james1236/pico-foldable/ssd1327.py

"""
MicroPython SSD1327 OLED I2C driver
https://github.com/mcauser/micropython-ssd1327

MIT License
Copyright (c) 2017 Mike Causer

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
from micropython import const
import time
import framebuf
from uos import uname


# commands
SET_COL_ADDR          = const(0x15)
SET_SCROLL_DEACTIVATE = const(0x2E)
SET_ROW_ADDR          = const(0x75)
SET_CONTRAST          = const(0x81)
SET_SEG_REMAP         = const(0xA0)
SET_DISP_START_LINE   = const(0xA1)
SET_DISP_OFFSET       = const(0xA2)
SET_DISP_MODE         = const(0xA4) # 0xA4 normal, 0xA5 all on, 0xA6 all off, 0xA7 when inverted
SET_MUX_RATIO         = const(0xA8)
SET_FN_SELECT_A       = const(0xAB)
SET_DISP              = const(0xAE) # 0xAE power off, 0xAF power on
SET_PHASE_LEN         = const(0xB1)
SET_DISP_CLK_DIV      = const(0xB3)
SET_SECOND_PRECHARGE  = const(0xB6)
SET_GRAYSCALE_TABLE   = const(0xB8)
SET_GRAYSCALE_LINEAR  = const(0xB9)
SET_PRECHARGE         = const(0xBC)
SET_VCOM_DESEL        = const(0xBE)
SET_FN_SELECT_B       = const(0xD5)
SET_COMMAND_LOCK      = const(0xFD)

# registers
REG_CMD  = const(0x80)
REG_DATA = const(0x40)


class SSD1327:
    def __init__(self, width, height, external_vcc):
        self.width = width
        self.height = height
        self.external_vcc = external_vcc
        self.buffer = bytearray(self.width * self.height // 2)
        self.framebuf = framebuf.FrameBuffer(self.buffer, self.width, self.height, framebuf.GS4_HMSB)
        self.poweron()
        self.init_display()

    def init_display(self):
        for cmd in (
            SET_COMMAND_LOCK, 0x12, # Unlock
            SET_DISP, # Display off
            # Resolution and layout
            SET_DISP_START_LINE, 0x00,
            SET_DISP_OFFSET, 0x20, # Set vertical offset by COM from 0~127
            # Set re-map
            # Enable column address re-map
            # Disable nibble re-map
            # Horizontal address increment
            # Enable COM re-map
            # Enable COM split odd even
            SET_SEG_REMAP, 0x51,
            SET_MUX_RATIO, self.height - 1,
            # Timing and driving scheme
            SET_FN_SELECT_A, 0x01, # Enable internal VDD regulator
            SET_PHASE_LEN, 0x51, # Phase 1: 1 DCLK, Phase 2: 5 DCLKs
            SET_DISP_CLK_DIV, 0x01, # Divide ratio: 1, Oscillator Frequency: 0
            SET_PRECHARGE, 0x08, # Set pre-charge voltage level: VCOMH
            SET_VCOM_DESEL, 0x07, # Set VCOMH COM deselect voltage level: 0.86*Vcc
            SET_SECOND_PRECHARGE, 0x01, # Second Pre-charge period: 1 DCLK
            SET_FN_SELECT_B, 0x62, # Enable enternal VSL, Enable second precharge
            # Display
            SET_GRAYSCALE_LINEAR, # Use linear greyscale lookup table
            SET_CONTRAST, 0x7f, # Medium brightness
            SET_DISP_MODE, # Normal, not inverted
            # 96x96:
            # SET_ROW_ADDR, 0 95,
            # SET_COL_ADDR, 8, 55,
            # 128x128:
            # SET_ROW_ADDR, 0 127,
            # SET_COL_ADDR, 0, 63,
            SET_ROW_ADDR, 0x00, self.height - 1,
            SET_COL_ADDR, ((128 - self.width) // 4), 63 - ((128 - self.width) // 4),

            SET_SCROLL_DEACTIVATE,
            SET_DISP | 0x01): # Display on
            self.write_cmd(cmd)
        self.fill(0)
        self.show()

    def poweroff(self):
        self.write_cmd(SET_FN_SELECT_A)
        self.write_cmd(0x00) # Disable internal VDD regulator, to save power
        self.write_cmd(SET_DISP)

    def poweron(self):
        self.write_cmd(SET_FN_SELECT_A)
        self.write_cmd(0x01) # Enable internal VDD regulator
        self.write_cmd(SET_DISP | 0x01)

    def rotate(self, rotate):
        self.poweroff()
        self.write_cmd(SET_DISP_OFFSET)
        self.write_cmd(self.height if rotate else self.offset)
        self.write_cmd(SET_SEG_REMAP)
        self.write_cmd(0x42 if rotate else 0x51)
        self.poweron()

    def contrast(self, contrast):
        self.write_cmd(SET_CONTRAST)
        self.write_cmd(contrast) # 0-255

    def invert(self, i):
        if (i == 0):
            i = 0xA4
        else:
            i = 0xA7
        self.write_cmd(SET_DISP_MODE | (i & 1) << 1 | (i & 1)) # 0xA4=Normal, 0xA7=Inverted

    def show(self):
        self.write_cmd(SET_COL_ADDR)
        self.write_cmd((128 - self.width) // 4)
        self.write_cmd(63 - ((128 - self.width) // 4))
        self.write_cmd(SET_ROW_ADDR)
        self.write_cmd(0x00)
        self.write_cmd(self.height - 1)
        self.write_data(self.buffer)

    def fill(self, col):
        self.framebuf.fill(col)

    def pixel(self, x, y, col):
        self.framebuf.pixel(x, y, col)
        
    def fill_rect(self, x, y, width, height, color):
        self.framebuf.fill_rect(x, y, width, height, color)

    def stroke_rect(self, x, y, width, height, color):
        self.framebuf.rect(x, y, width, height, color) #stroke_rect, or rect with f = False
        
    def blit(self, buffer, x, y, key, palette=None):
        if (palette == None):
            self.framebuf.blit(buffer, x, y, key)
        else:
            self.framebuf.blit(buffer, x, y, key, palette)

    def scroll(self, dx, dy):
        self.framebuf.scroll(dx, dy)
        # software scroll

    def text(self, string, x, y, col=15):
        self.framebuf.text(string, x, y, col)

    def line(self, x1, y1, x2, y2, col):
        self.framebuf.line(x1, y1, x2, y2, col)

    #Given a list of coordinates, draw an arbitrary (convex or concave) closed polygon at the given x, y location using the given color.
    #The coords must be specified as a array of integers, e.g. array('h', [x0, y0, x1, y1, ... xn, yn]).
    #The optional fill parameter can be set to True to fill the polygon. Otherwise just a one pixel outline is drawn.
    def poly(self, x, y, coords, col, fill=False):
        self.framebuf.poly(x, y, coords, col, fill)

    #Draw an ellipse at the given location. Radii xr and yr define the geometry; equal values cause a circle to be drawn. The c parameter defines the color.
    #The optional fill parameter can be set to True to fill the ellipse. Otherwise just a one pixel outline is drawn.
    #The optional quadrantBits parameter enables drawing to be restricted to certain quadrants of the ellipse.
    #The LS four bits determine which quadrants are to be drawn, with bit 0 specifying Q1, b1 Q2, b2 Q3 and b3 Q4.
    #Quadrants are numbered counterclockwise with Q1 being top right.
    def ellipse(self, x, y, xr, yr, col, fill=False, quadrantBits=0xF):
        self.framebuf.ellipse(x, y, xr, yr, col, fill, quadrantBits)


class SSD1327_I2C(SSD1327):
    def __init__(self, width, height, i2c, addr=0x3c, external_vcc=False):
        self.i2c = i2c
        self.addr = addr
        self.temp = bytearray(2)
        super().__init__(width, height, external_vcc)

    def write_cmd(self, cmd):
        self.temp[0] = REG_CMD # Co=1, D/C#=0
        self.temp[1] = cmd
        self.i2c.writeto(self.addr, self.temp)

    def write_data(self, buf):
        self.temp[0] = self.addr << 1
        self.temp[1] = REG_DATA # Co=0, D/C#=1
        # check if board is Pi Pico as it doesn't support start, write and stop operations.
        if uname()[0] == 'rp2':
            self.i2c.writeto(self.addr, b'\x40' + buf)
        else:
            self.i2c.start()
            self.i2c.write(self.temp)
            self.i2c.write(buf)
            self.i2c.stop()


class SEEED_OLED_96X96(SSD1327_I2C):
    def __init__(self, i2c):
        super().__init__(96, 96, i2c)

    def rotate(self, rotate):
        self.poweroff()
        self.write_cmd(SET_DISP_OFFSET)
        self.write_cmd(0x60 if rotate else 0x20) # 0x20=0 degrees, 0x60=180 degrees
        self.write_cmd(SET_SEG_REMAP)
        self.write_cmd(0x42 if rotate else 0x51) # 0x51=0 degrees, 0x42=180 degrees
        self.poweron()

    def lookup(self, table):
        # GS0 has no pre-charge and current drive
        self.write_cmd(SET_GRAYSCALE_TABLE)
        for i in range(0,15):
            self.write_cmd(table[i])


class WS_OLED_128X128(SSD1327_I2C):
    def __init__(self, i2c, addr=0x3c):
        super().__init__(128, 128, i2c, addr)
        self.write_cmd(SET_DISP_OFFSET)
        self.write_cmd(0x00)
