james1236/pico-foldable/creations/dog.py

from buzzer_music import music
import utime
import _thread
import framebuf

musicPlaying = False
mySong = None

def musicThread():
    global mySong
    global musicPlaying
    
    while True:
        utime.sleep(0.04)
        if (not musicPlaying):
            mySong.stop()
            del mySong
            break
        
        try:
            mySong.tick()
        except Exception:
            pass

#Optional metadata for main menu
class description:
    name = "Dog :)"
    thumbnail = bytearray(b"\x00\x00\x00\x00\x00\x00\x00\x00\x00\x00\x00\x00\x00\x00\x00\x00\x00\x00\x00\x00\x00\x00\x00\x00\x00\x00\x00\x00\x00\xbd\x00\x00\x01\x42\x80\x00\x01\x00\x80\x00\x01\x00\x40\x80\x02\x48\x61\x40\x02\x00\x19\x40\x02\x30\x07\x40\x02\xa4\x00\x40\x02\x78\x00\x40\x02\x00\x00\x40\x02\x00\x00\x40\x02\x00\x00\x40\x02\x00\x00\x40\x01\x00\x00\x80\x01\x33\xcc\x80\x01\x32\x4c\x80\x01\x54\x55\x00\x00\x88\x22\x00\x00\x00\x00\x00\x00\x00\x00\x00\x00\x00\x00\x00\x00\x00\x00\x00\x00\x00\x00\x00\x00\x00\x00\x00\x00\x00\x00\x00")

#Required class named 'creation'
class creation:
    def __init__(self, display, controller, *args): #Required init method in creation class
        global mySong
        global musicPlaying
        self.frame = 0
        self.display = display
        self.controller = controller
        
        data = bytearray(b"\x88\xa8\x8a\x8a\x8a\x8a\xaa\xaa\x8a\xaa\xaa\xaa\xaa\xaa\xaa\xaa\xaa\xaa\xaa\xaa\xaa\xaa\xaa\xaa\xaa\xaa\xaa\xaa\xaa\xaa\xaa\xaa\xaa\xaa\xaa\xaa\xaa\xaa\xaa\xaa\xaa\xaa\xaa\xaa\x8a\xa8\xa8\xa8\xa8\xa8\x8a\x88\x88\x88\x88\x88\x88\x88\x88\x88\x88\x88\x88\x88\xa8\x8a\x8a\x8a\x8a\xa8\xa8\xaa\xaa\x8a\xaa\xaa\xaa\xaa\xaa\xaa\xaa\xaa\xaa\xaa\xaa\xaa\xaa\xaa\xaa\xaa\xaa\xaa\xaa\xaa\xaa\xaa\xaa\xaa\xaa\xaa\xaa\xaa\xa8\xaa\x8a\x8a\x8a\x8a\xa8\xaa\xa8\xa8\xa8\x8a\x88\x8a\x88\x88\x88\x88\x88\x88\x88\x88\x88\x88\x88\x88\x88\xa8\xa8\xa8\xaa\x8a\xaa\xaa\xa8\xaa\xaa\xaa\xaa\xaa\xaa\xaa\xaa\xaa\xaa\xaa\xaa\xaa\xaa\xaa\xaa\xaa\xaa\xaa\xaa\xaa\xaa\xaa\xaa\xaa\xaa\xaa\xaa\xaa\xaa\xaa\xaa\xaa\xaa\xaa\x8a\xa8\x8a\x8a\x8a\x8a\x88\x8a\x88\x88\x88\x88\x88\x88\x88\x88\x88\x88\x88\x88\x8a\x8a\x8a\x8a\x8a\x8a\x8a\xaa\xaa\xaa\xaa\xaa\xaa\xaa\xaa\xaa\xaa\xaa\xaa\xaa\xaa\xaa\xaa\xaa\xaa\xaa\xaa\xaa\xaa\xaa\xaa\xaa\xaa\xaa\xaa\xaa\xaa\xa8\xaa\xaa\xaa\x8a\xa8\xaa\xa8\xaa\xa8\xa8\x8a\x88\xa8\x88\x88\x88\x88\x88\x88\x88\x88\x88\x88\x88\x88\x88\x8a\x8a\x8a\xaa\x8a\xaa\xaa\xa8\xaa\xaa\xaa\xaa\xaa\xaa\xaa\xaa\xaa\xaa\xaa\xaa\xaa\xaa\xaa\xaa\xaa\xaa\xaa\xaa\xaa\xaa\xaa\xaa\xaa\xaa\xaa\xaa\xaa\xaa\xaa\xaa\xa8\xaa\xaa\xa8\xa8\xa8\x8a\x8a\x8a\x88\xa8\x88\x88\x88\x88\x88\x88\x88\x88\x88\x88\x88\x88\x88\x8a\x8a\x8a\x8a\xaa\xa8\xaa\xaa\xaa\xaa\xaa\xaa\xaa\xaa\xaa\xaa\xaa\xaa\xaa\xaa\xaa\xaa\xaa\xaa\xaa\xaa\xaa\xaa\xaa\xaa\xaa\xaa\xaa\xaa\xaa\xaa\xaa\xaa\xaa\xaa\xaa\xaa\x8a\xaa\x8a\xa8\xa8\xa8\x8a\x88\x8a\x88\x88\x88\x88\x88\x88\x88\x88\x88\x88\x88\x88\x88\x8a\x8a\xaa\x8a\xa8\xaa\xaa\xaa\xaa\xaa\xaa\xaa\xaa\xaa\xaa\xaa\xaa\xaa\xaa\xaa\xaa\xaa\xaa\xaa\xaa\xaa\xaa\xaa\xaa\xaa\xaa\xaa\xaa\xaa\xaa\xaa\xaa\xaa\xaa\xaa\xaa\xaa\x8a\xa8\xaa\x8a\x8a\x8a\x8a\x8a\x88\x88\x88\x88\x88\x88\x88\x88\x88\x88\x88\x88\x88\x88\xa8\xa8\xaa\xaa\xaa\xaa\xaa\xaa\xaa\xaa\xaa\xaa\xaa\xaa\xaa\xaa\xaa\xaa\xaa\xaa\xaa\xaa\xaa\xaa\xaa\xaa\xaa\xaa\xaa\xaa\xaa\xa8\xaa\xaa\xaa\xaa\xaa\xaa\xaa\xaa\xaa\xaa\xaa\xaa\x8a\xaa\x8a\x8a\x88\x8a\x88\xa8\x88\x88\x88\x88\x88\x88\x88\x88\x88\x88\x88\x88\xa8\xaa\xa8\xaa\xaa\xaa\xaa\xaa\xaa\xaa\xaa\xaa\xaa\xaa\xaa\xaa\xaa\xaa\xaa\xaa\xaa\xaa\xaa\xaa\xaa\xaa\xaa\xaa\xbb\xbc\xbb\xcc\xec\xec\xcc\xcb\xba\xaa\xaa\xaa\xaa\xaa\xaa\xaa\x8a\xa8\xaa\x88\xa8\xa8\x88\x88\x88\x88\x88\x88\x88\x88\x88\x88\x88\x88\x88\x88\xa8\xaa\xaa\x8a\xaa\xaa\xaa\xaa\xaa\xaa\xaa\xaa\xaa\xaa\xaa\xaa\xaa\xaa\xaa\xaa\xaa\xaa\xaa\xaa\xaa\xac\xce\xee\xef\xff\xff\xfe\xef\xff\xef\xff\xfe\xee\xcc\xba\xaa\xaa\xaa\xaa\xaa\xaa\x8a\x8a\xa8\x8a\x8a\x88\x88\x88\x88\x88\x88\x88\x88\x88\x88\x88\x88\x88\xaa\xaa\xaa\xaa\xaa\xaa\xaa\xaa\xaa\xaa\xaa\xaa\xaa\xaa\xaa\xaa\xaa\xaa\xaa\xaa\xaa\xaa\xaa\xbc\xee\xee\xee\xee\xee\xee\xfe\xee\xfe\xee\xee\xee\xef\xee\xff\xfe\xeb\xaa\xaa\xaa\xa8\xaa\x8a\xab\xa8\xaa\xa8\x88\x88\x88\x88\x88\x88\x88\x88\x88\x88\x88\x88\x87\x8a\xaa\xaa\xaa\xaa\xaa\xaa\xaa\xaa\xaa\xaa\xaa\xaa\xaa\xaa\xaa\xaa\xaa\xaa\xaa\xaa\xaa\xbe\xee\xee\xee\xee\xee\xee\xee\xee\xee\xee\xee\xee\xfe\xee\xfe\xee\xee\xff\xfe\xba\xaa\xba\xaa\xab\xbb\xaa\xab\xaa\xa8\x88\x88\x88\x88\x88\x88\x88\x88\x88\x88\x88\x88\xaa\xaa\xaa\xaa\xaa\xaa\xaa\xaa\xaa\xaa\xaa\xaa\xaa\xaa\xaa\xbb\xaa\xaa\xaa\xaa\xaa\xce\xee\xee\xee\xee\xee\xee\xee\xee\xee\xee\xee\xee\xee\xee\xfe\xee\xee\xee\xee\xee\xff\xee\xcb\xaa\xbe\xee\xee\xec\xaa\xa8\x88\x88\x88\x88\x88\x88\x88\x88\x88\x88\x88\x77\xaa\xaa\xaa\xaa\xaa\xaa\xaa\xaa\xaa\xaa\xaa\xaa\xaa\xab\xba\xce\xca\xaa\xaa\xaa\xac\xee\xee\xee\xee\xee\xee\xee\xee\xee\xee\xee\xee\xee\xee\xee\xee\xef\xef\xef\xee\xfe\xee\xef\xee\xee\xef\xee\xee\xee\xcb\xaa\x88\x88\x88\x88\x88\x88\x88\x88\x88\x88\x78\x87\xaa\xaa\xaa\xaa\xaa\xaa\xaa\xaa\xaa\xaa\xaa\xaa\xbb\xcc\xcc\xee\xec\xce\xeb\xab\xce\xee\xee\xee\xee\xee\xee\xee\xee\xee\xee\xee\xee\xee\xee\xee\xef\xee\xfe\xef\xee\xee\xef\xef\xee\xef\xee\xee\xee\xee\xee\xba\xa8\x88\x88\x88\x88\x88\x88\x88\x88\x78\x78\x78\xaa\xaa\xaa\xaa\xaa\xaa\xaa\xaa\xaa\xaa\xaa\xaa\xbb\xce\xee\xee\xfe\xef\xee\xee\xee\xee\xee\xee\xee\xee\xee\xee\xee\xee\xee\xee\xee\xee\xee\xef\xee\xfe\xef\xef\xef\xef\xee\xfe\xef\xee\xee\xee\xee\xee\xee\xec\xb8\xaa\x88\x88\x88\x88\x88\x88\x88\x78\x78\x77\xaa\xaa\xaa\xaa\xaa\xaa\xaa\xaa\xaa\xaa\xaa\xab\xbb\xce\xee\xee\xee\xee\xfe\xee\xee\xee\xee\xee\xee\xee\xee\xee\xee\xee\xee\xee\xee\xee\xee\xee\xee\xfe\xff\xee\xfe\xef\xef\xee\xfe\xef\xef\xee\xee\xee\xee\xee\xca\x88\x88\x88\x88\x88\x88\x88\x88\x78\x78\x77\xaa\xaa\xaa\xaa\xaa\xaa\xaa\xaa\xaa\xaa\xab\xcc\xcc\xee\xee\xee\xee\xee\xee\xee\xee\xee\xee\xee\xee\xee\xee\xee\xee\xee\xfe\xee\xee\xee\xee\xee\xee\xef\xef\xef\xee\xfe\xfe\xfe\xef\xee\xfe\xee\xee\xee\xee\xee\xee\xb8\x88\x88\x88\x88\x88\x88\x78\x87\x78\x77\xaa\xaa\xaa\xaa\xaa\xaa\xaa\xaa\xaa\xaa\xbc\xce\xee\xee\xee\xee\xee\xee\xee\xee\xee\xee\xee\xee\xee\xee\xee\xee\xee\xee\xfe\xee\xee\xee\xee\xee\xee\xfe\xef\xef\xef\xee\xff\xee\xee\xef\xee\xfe\xee\xee\xee\xee\xee\xeb\x88\x88\x88\x88\x88\x87\x88\x77\x78\x77\xaa\xaa\xaa\xaa\xaa\xaa\xaa\xaa\xaa\xaa\xbb\xcc\xee\xee\xee\xee\xee\xee\xee\xee\xee\xee\xee\xee\xee\xee\xee\xee\xee\xee\xee\xee\xee\xee\xee\xee\xee\xef\xef\xee\xfe\xfe\xef\xfe\xfe\xee\xfe\xee\xee\xee\xee\xee\xee\xee\xa8\x88\x88\x88\x88\x88\x78\x78\x77\x77\xaa\xaa\xaa\xaa\xaa\xaa\xaa\xaa\xaa\xaa\xbb\xce\xee\xee\xee\xee\xee\xee\xee\xee\xee\xee\xee\xee\xee\xee\xee\xee\xee\xee\xee\xfe\xee\xee\xee\xfe\xee\xee\xee\xfe\xfe\xfe\xfe\xee\xfe\xee\xee\xef\xee\xee\xee\xee\xee\xee\xea\x88\x88\x88\x87\x78\x78\x78\x77\x77\xaa\xaa\xaa\xaa\xaa\xaa\xaa\xaa\xab\xbc\xce\xce\xee\xee\xee\xee\xee\xee\xee\xee\xec\xee\xee\xee\xee\xee\xee\xee\xee\xee\xee\xee\xee\xee\xee\xee\xef\xee\xee\xee\xee\xfe\xfe\xfe\xfe\xee\xfe\xee\xee\xee\xee\xee\xee\xee\xee\xa8\x88\x88\x88\x88\x78\x77\x77\x77\xaa\xaa\xaa\xaa\xaa\xaa\xaa\xaa\xbb\xee\xee\xee\xce\xce\xee\xee\xee\xee\xee\xce\xce\xcc\xce\xee\xee\xee\xee\xee\xee\xfe\xee\xee\xee\xee\xee\xee\xee\xee\xee\xfe\xef\xee\xfe\xfe\xee\xee\xee\xee\xee\xee\xee\xee\xee\xee\xee\xee\xba\x88\x88\x87\x78\x77\x77\x77\xaa\xaa\xaa\xaa\xaa\xaa\xaa\xbb\xce\xee\xee\xee\xee\xce\xce\xee\xee\xee\xce\xce\xce\xee\xce\xce\xee\xee\xee\xee\xee\xee\xee\xee\xee\xee\xee\xee\xee\xee\xee\xee\xee\xee\xfe\xef\xfe\xfe\xee\xee\xee\xee\xee\xee\xee\xee\xee\xee\xec\xa8\x87\x78\x77\x87\x77\x77\xaa\xaa\xaa\xaa\xaa\xab\xab\xcc\xee\xee\xcc\xcc\xce\xce\xce\xee\xee\xee\xce\xcc\xce\xee\xee\xee\xce\xec\xee\xee\xee\xee\xee\xee\xee\xee\xee\xee\xee\xee\xee\xee\xee\xfe\xfe\xef\xee\xee\xee\xee\xee\xee\xee\xee\xee\xee\xee\xee\xee\xeb\xaa\xbb\xcb\xcb\x87\x77\xaa\xaa\xaa\xaa\xaa\xab\xcc\xee\xec\xcc\xcc\xcc\xcc\xee\xee\xee\xce\xec\xcc\xcc\xcc\xce\xce\xee\xee\xee\xee\xee\xee\xee\xee\xee\xee\xee\xee\xee\xee\xee\xee\xee\xee\xee\xee\xee\xfe\xee\xee\xee\xee\xee\xee\xee\xee\xee\xee\xee\xee\xee\xee\xee\xcc\xba\xa8\x77\xaa\xaa\xaa\xab\xab\xbc\xce\xec\xcc\xcc\xcc\xcc\xcc\xce\xee\xee\xec\xcc\xcb\xcb\xcc\xce\xcc\xce\xee\xce\xee\xee\xee\xee\xee\xee\xee\xee\xee\xee\xee\xee\xee\xee\xee\xfe\xef\xee\xee\xee\xee\xee\xee\xee\xee\xee\xee\xee\xec\xcc\xee\xee\xee\xee\xee\xcb\xaa\x87\xaa\xaa\xaa\xab\xab\xbe\xec\xcc\xcb\xbb\xbb\xcc\xcc\xcc\xcc\xcc\xec\xcb\xcb\xcc\xce\xcc\xcc\xcc\xee\xce\xee\xee\xee\xee\xee\xee\xee\xcc\xee\xee\xee\xee\xee\xee\xfe\xef\xee\xee\xee\xee\xee\xee\xee\xee\xee\xee\xee\xec\xcc\xec\xee\xee\xee\xee\xee\xcc\xaa\xaa\xaa\xaa\xaa\xbb\xcc\xee\xec\xbb\xbb\xbc\xbc\xcb\xcc\xbc\xcc\xbb\xbb\xcb\xcb\xcc\xcc\xcb\xcc\xcc\xcc\xee\xee\xee\xee\xee\xee\xee\xee\xec\xee\xee\xee\xee\xee\xee\xef\xee\xee\xee\xee\xee\xee\xee\xee\xee\xee\xee\xee\xec\xcc\xcc\xee\xee\xee\xec\xcc\xee\xec\xa8\xaa\xab\xaa\xbc\xee\xee\xcc\xba\xbb\xbb\xab\xbb\xbc\xcc\xbc\xbc\xcb\xbb\xbc\xcc\xcc\xcc\xcb\xcc\xce\xee\xce\xee\xee\xee\xec\xee\xee\xee\xee\xee\xee\xee\xee\xfe\xff\xee\xee\xee\xee\xee\xee\xee\xee\xce\xee\xee\xee\xee\xcb\xcc\xec\xee\xee\xee\xcc\xee\xcc\xba\xaa\xba\xbc\xee\xec\xcc\xbb\xab\xaa\xaa\xab\xbb\xbb\xba\xbb\xbb\xaa\xbb\xbc\xbb\xba\xbb\xcc\xcc\xee\xee\xee\xee\xee\xee\xec\xee\xec\xec\xee\xee\xee\xee\xee\xee\xef\xee\xee\xee\xee\xee\xee\xee\xee\xce\xce\xce\xee\xee\xcc\xcb\xce\xcc\xcc\xec\xcc\xce\xec\xba\xcc\xee\xee\xcc\xcb\xbb\xaa\xaa\xaa\xaa\xab\xbb\xba\xbb\xaa\xaa\xaa\xab\xbb\xaa\xba\xba\xbb\xcc\xee\xee\xee\xee\xee\xee\xee\xee\xee\xec\xee\xee\xee\xee\xee\xef\xee\xfe\xee\xfe\xfe\xee\xee\xee\xee\xcc\xee\xee\xec\xee\xcc\xcb\xbc\xee\xcc\xce\xce\xcc\xee\xca\xee\xec\xcb\xcb\xbb\xbb\xaa\xaa\xaa\xaa\xab\xbb\xbb\xbc\xbc\xba\xaa\xaa\xba\xab\xab\xbc\xce\xee\xee\xee\xee\xee\xfe\xee\xee\xee\xee\xee\xee\xee\xee\xee\xee\xee\xee\xfe\xee\xee\xfe\xee\xee\xee\xee\xcc\xcb\xcb\xcc\xce\xec\xcb\xbb\xbe\xcc\xcb\xcc\xcc\xce\xec\xcc\xcc\xcb\xba\xab\xaa\xab\xaa\x8a\x88\xab\xaa\xaa\xba\xaa\xa8\x8a\xaa\xaa\xaa\xaa\xbc\xcc\xee\xce\xee\xee\xfe\xee\xee\xee\xee\xee\xee\xee\xee\xee\xee\xee\xee\xee\xee\xee\xef\xef\xee\xee\xee\xee\xec\xce\xec\xce\xce\xcc\xcc\xba\xbb\xcc\xbb\xbc\xbc\xcc\xcc\xcc\xcb\xaa\x8a\xaa\xaa\xaa\x88\x88\x8a\xbb\xab\xaa\x88\x88\x8a\xaa\xba\xba\xbb\xbc\xcc\xee\xee\xec\xee\xee\xee\xee\xee\xfe\xee\xee\xee\xee\xee\xee\xee\xee\xee\xee\xee\xee\xee\xfe\xfe\xee\xee\xee\xee\xca\xbb\xce\xee\xcc\xcc\xbb\xab\xbc\xca\xac\xcb\xbb\xcc\xcb\xba\xaa\xaa\x88\x8a\xa8\x8a\x88\x8a\xbb\xaa\xaa\x88\x8a\xaa\xaa\xbb\xba\xab\xbc\xee\xee\xec\xcc\xbe\xee\xee\xee\xef\xef\xee\xee\xee\xee\xee\xee\xee\xee\xee\xee\xee\xee\xee\xee\xfe\xee\xee\xee\xee\xce\xcc\xbc\xce\xee\xca\xcb\xab\xbb\xca\x8a\xbc\xbc\xbb\xba\xa8\x88\x88\x8a\xaa\x88\xa8\x88\xaa\xaa\xaa\xba\xbb\xba\x8a\xab\xaa\xab\xbb\xce\xee\xee\xee\xcb\xbc\xce\xee\xee\xee\xee\xee\xee\xee\xee\xee\xee\xee\xee\xee\xee\xee\xcc\xee\xee\xee\xff\xee\xee\xee\xcb\xbc\xce\xce\xec\xeb\xac\xca\xab\xbb\xaa\xbb\xbb\xbc\xba\x88\x88\x88\x8a\xaa\x8a\xa8\x8a\xaa\xab\xba\xaa\xbb\xa8\x8a\xab\xbb\xab\xcc\xce\xee\xee\xcb\xba\xab\xcc\xee\xee\xee\xee\xee\xee\xee\xee\xee\xee\xee\xee\xee\xee\xee\xcb\xee\xee\xee\xee\xee\xee\xee\xec\xbc\xce\xee\xcc\xec\xbb\xcb\xab\xcb\xaa\xab\xaa\xac\xaa\x88\x88\x88\xaa\xa8\x8a\x8a\xa8\xa8\xab\xaa\xbe\xb8\x88\x8a\xbb\xab\xbb\xbc\xce\xee\xce\xcb\xba\xaa\xab\xee\xee\xee\xee\xee\xee\xee\xee\xee\xee\xee\xee\xec\xec\xcc\xab\xcc\xce\xee\xee\xfe\xee\xee\xec\xbb\xce\xee\xcc\xcc\xcb\xbc\xba\xbb\xba\xab\xbb\xab\xaa\x88\x88\x8a\xaa\x88\xa8\x8a\xa8\xa8\xaa\xab\xba\xaa\x87\x8b\xba\xab\xbb\xce\xee\xee\xec\xab\xaa\xaa\x8b\xce\xee\xee\xee\xee\xee\xee\xec\xee\xee\xee\xee\xec\xcc\xbb\xaa\xaa\xcc\xee\xee\xee\xee\xee\xee\xcb\xae\xee\xec\xcc\xcc\xbb\xba\xbb\xba\xaa\xbb\xab\xa8\x88\x8a\xaa\x88\x88\xa8\xa8\x8a\xaa\xaa\xaa\xbb\xa8\x87\xaa\xaa\xba\xbb\xee\xce\xee\xcb\xba\x88\x88\x8a\xbc\xce\xee\xee\xee\xee\xee\xec\xee\xee\xee\xee\xec\xbb\xaa\xa8\x88\xa8\xac\xee\xee\xee\xee\xee\xbb\xbc\xee\xce\xbc\xcc\xcb\xba\xbb\xba\xab\xbc\xbb\xa8\x88\x8a\xa8\x88\x88\x88\xa8\xaa\xaa\xaa\xaa\xaa\xa8\x67\xaa\xaa\xab\xbc\xce\xcc\xcb\xca\xaa\x84\x86\x88\xaa\xcc\xee\xee\xee\xee\xee\xee\xee\xee\xee\xee\xec\xba\xa8\x86\x66\x8a\xba\xbe\xee\xee\xee\xec\xba\xbc\xce\xee\xcc\xcc\xcc\xbb\xbb\xba\xab\xbb\xcb\x88\x8a\xaa\xa8\x88\xa8\x8a\x8a\xaa\xaa\xaa\xaa\xaa\x87\x48\xba\xba\xbb\xbc\xcc\xba\xa8\x88\x88\x86\x67\x88\xab\xbc\xee\xef\xef\xee\xee\xee\xee\xee\xee\xee\xee\xca\x88\x74\x22\x66\x8e\xcc\xee\xee\xee\xee\xaa\xcb\xce\xee\xeb\xeb\xcc\xbb\xab\xba\xaa\xbb\xbc\x88\x8a\xaa\x88\x88\x88\x8a\x8a\xaa\xaa\xaa\xaa\xba\x86\x6a\xaa\xab\xbb\xbc\xbb\xba\xaa\xca\xa7\x66\x46\x78\xaa\xbe\xef\xef\xff\xee\xee\xee\xee\xee\xee\xee\xee\xbb\x88\x61\x67\x41\x14\xce\xcc\xee\xee\xee\xb8\xbc\xce\xee\xec\xcb\xcb\xbb\xbb\xaa\xaa\xbc\xbc\x8a\xaa\xaa\xa8\xa8\x88\x8a\xaa\xaa\xaa\xab\xab\xb8\x74\x8a\xab\xaa\xbb\xbc\xba\xaa\xce\x41\x11\x11\x44\x78\xaa\xee\xee\xef\xfe\xef\xee\xee\xee\xee\xee\xee\xee\xeb\x87\x42\x8a\x64\x11\x6e\xec\xee\xee\xce\xb8\x8a\xce\xee\xcc\xcb\xbb\xba\xba\xaa\xaa\xaa\xbc\x88\x8a\xaa\x88\xa8\x88\x8a\xaa\xaa\xaa\xab\xbb\xa8\x66\x8a\xab\xab\xba\xba\xaa\xac\xb4\x11\x14\x74\x24\x48\x8c\xee\xee\xef\xff\xef\xee\xee\xee\xee\xfe\xee\xee\xec\xc7\x22\x11\x41\x21\x2a\xee\xcc\xee\xec\xa7\xaa\xbc\xee\xec\xcb\xbb\xba\xaa\xaa\xaa\xba\xab\x88\x88\xaa\x8a\xa8\x88\x8a\xaa\xaa\xba\xbb\xbb\x88\x67\x8a\xaa\xaa\xab\xbb\xaa\xbc\x41\x14\x66\xab\x42\x48\x8c\xee\xee\xef\xff\xef\xee\xee\xfe\xfe\xee\xee\xef\xee\xeb\x22\x11\x11\x21\x16\xac\xbb\xce\xcc\xb6\x88\xcc\xce\xec\xbb\xab\xba\xaa\xaa\xaa\xaa\xbb\x88\x88\x8a\x8a\xa8\x88\x8a\xaa\xab\xab\xbb\xa8\x87\x68\x8a\xaa\xaa\xab\xba\xab\xb7\x11\x24\x42\x47\x41\x48\xee\xee\xee\xee\xff\xef\xfe\xee\xff\xff\xff\xff\xee\xee\xee\x84\x21\x11\x12\x47\xab\xbb\xbb\xbc\xb6\x78\xac\xce\xec\xbb\xba\xaa\xaa\xaa\xaa\xaa\xab\x88\x88\x88\x8a\x88\xaa\x8a\xaa\xaa\xab\xbb\x8a\x87\x48\x8a\x8a\xaa\xab\xaa\xaa\x82\x12\x41\x11\x12\x12\x7b\xbc\xfe\xee\xee\xff\xff\xfe\xef\xff\xff\xff\xff\xef\xee\xee\xe7\x44\x44\x44\x7a\xce\xba\xab\xbc\xb6\x48\x8b\xcc\xec\xcb\xba\x8a\xab\xaa\xaa\xab\xbb\x88\x88\x88\x88\x88\x8a\x8a\xaa\xaa\xbb\xba\x8a\x87\x68\x88\x8a\xaa\xaa\x88\x87\x42\x11\x12\x11\x11\x17\xbe\xee\xee\xee\xff\xff\xff\xef\xef\xfe\xff\xff\xff\xfe\xff\xee\xee\xa7\x46\x68\xac\xce\xca\xbb\xcc\xb6\x48\x88\xbc\xee\xcb\xba\xaa\xaa\xba\xaa\xaa\xba\x88\x88\x77\x88\x88\x8a\x8a\xaa\xaa\xbb\xba\x8a\x84\x48\x88\x8a\xaa\x88\x87\x87\x64\x44\x21\x12\x44\x8a\xbe\xee\xef\xfe\xff\xff\xff\xfe\xef\xfe\xff\xff\xff\xff\xfe\xee\xfe\xeb\xaa\xab\xbe\xee\xec\xce\xec\xb6\x26\x87\xab\xee\xcc\xaa\xaa\xba\xab\xaa\xaa\xba\x88\x78\x87\x77\x87\x88\x8a\x8a\xaa\xbb\xba\x78\x84\x48\x88\xa8\x88\x88\x8a\xaa\xa8\x77\x76\x77\x77\x8a\xee\xce\xee\xef\xef\xff\xff\xfe\xff\xff\xff\xff\xff\xff\xff\xfe\xee\xec\xbb\xbe\xee\xee\xee\xee\xee\xc6\x24\x87\x8a\xce\xec\xba\xaa\xaa\xaa\xaa\xab\xba\x88\x88\x77\x77\x77\x88\x88\x8a\xaa\xbb\xa8\x77\x62\x68\x8a\x88\x88\x88\xaa\xaa\xaa\x88\x88\x87\x88\xac\xee\xee\xfe\xef\xff\xff\xef\xee\xff\xff\xff\xff\xff\xff\xff\xff\xfe\xee\xcc\xbc\xee\xee\xee\xee\xee\xc4\x24\x77\x8a\xbe\xec\xcb\xab\xaa\xaa\xaa\xab\xba\x86\x67\x77\x68\x77\x78\x88\x8a\xaa\xbb\xa8\x47\x62\x47\x8a\x8a\xaa\xaa\xaa\xaa\xaa\xbb\xaa\xaa\xab\xec\xee\xee\xee\xff\xff\xff\xfe\xff\xff\xff\xff\xff\xff\xff\xff\xff\xee\xee\xee\xcc\xee\xee\xee\xee\xee\xe6\x22\x66\x78\xbe\xec\xbb\x8a\xaa\x8a\xab\xaa\xba\x77\x78\x78\x78\x77\x88\x88\xaa\xbb\xbb\xa7\x47\x44\x48\x8a\xaa\xaa\xaa\xaa\xaa\xab\xba\xbb\xba\xbb\xcc\xee\xee\xef\xff\xff\xff\xff\xfe\xff\xff\xff\xfe\xee\xef\xff\xff\xef\xee\xee\xee\xee\xee\xee\xee\xee\xe8\x24\x44\x68\xac\xec\xba\x88\x8a\xaa\xab\xaa\xb8\x87\x76\x67\x78\x77\x78\x88\xaa\xbb\xbb\x86\x46\x44\x47\x8a\xaa\xaa\xba\xaa\xaa\xbb\xbb\xbb\xcc\xcc\xce\xee\xee\xff\xff\xff\xff\xee\xff\xff\xff\xee\xef\xee\xee\xef\xff\xee\xee\xee\xee\xee\xee\xee\xee\xee\xea\x44\x44\x67\x8b\xee\xba\x88\x88\xaa\xab\xaa\xa8\x87\x76\x67\x77\x78\x88\x88\xab\xba\xba\x86\x66\x44\x47\x8a\xaa\xbb\xcb\xba\xab\xbb\xba\xac\xcc\xcc\xce\xee\xee\xfe\xff\xff\xff\xff\xfe\xee\xee\xee\xee\xef\xee\xef\xef\xff\xee\xee\xef\xee\xee\xee\xee\xee\xea\x26\x64\x47\x8a\xee\xca\x88\x88\xaa\xab\xaa\x88\x88\x76\x67\x78\x88\x88\x8a\xab\xbb\xb8\x87\x64\x44\x46\x8a\xbb\xbb\xbb\xbb\xab\xaa\xab\xce\xec\xce\xce\xee\xef\xee\xee\xfe\xee\xee\xee\xec\xcc\xbb\xce\xee\xee\xee\xee\xff\xff\xee\xef\xee\xee\xee\xee\xef\xeb\x44\x76\x47\x8a\xce\xeb\x88\x88\xaa\xab\xba\x88\xa8\x76\x66\x76\x78\x88\x8a\xbb\xba\xb8\x86\x64\x44\x47\xaa\xab\xbb\xbb\xbb\xaa\xaa\xbc\xec\xcc\xcc\xcc\xee\xee\xee\xef\xff\xfe\xec\xbb\xbb\xaa\x8a\xaa\xce\xee\xee\xee\xff\xfe\xee\xee\xef\xfe\xee\xee\xee\xee\x44\x47\x46\x7a\xbe\xeb\xa8\x88\xab\xbb\xa8\x88\xa8\x87\x66\x67\x77\x88\xab\xbb\xbb\xa8\x76\x44\x44\x47\xab\xbc\xbc\xbb\xba\xba\xab\xcc\xcb\xce\xcc\xcc\xee\xee\xee\xee\xee\xee\xca\xa8\x87\x77\x88\x88\xac\xee\xce\xee\xef\xff\xee\xee\xee\xee\xee\xee\xee\xee\x64\x46\x44\x78\xbe\xec\xa8\xaa\xab\xba\xa8\x88\xba\x88\x66\x67\x77\x88\xaa\xbb\xbb\xa7\x74\x44\x44\x78\xaa\xbb\xbc\xbb\xab\xab\xbc\xcb\xce\xec\xcc\xce\xee\xee\xee\xec\xee\xec\xa8\x67\x66\x76\x64\x66\x78\xab\xcc\xee\xef\xff\xee\xee\xee\xef\xee\xee\xee\xee\x74\x46\x64\x68\xac\xec\xba\xaa\xbb\xba\xa8\x88\xba\xa8\x76\x66\x67\x88\xab\xbb\xbb\x88\x74\x44\x44\x8a\xaa\xbb\xba\xbb\xbb\xbb\xbb\xcc\xee\xec\xbb\xce\xee\xee\xee\xeb\xbc\xb8\x66\x66\x66\x66\x64\x46\x77\x68\xcc\xee\xef\xff\xfe\xee\xee\xee\xee\xee\xee\xee\x82\x47\x76\x67\xac\xee\xba\xab\xbb\xba\x88\x88\xba\xa8\x77\x66\x68\x88\xac\xbb\xba\x88\x74\x44\x46\x88\xab\xbb\xbb\xba\xab\xbb\xcc\xce\xec\xcb\xbc\xee\xee\xfe\xee\xee\xcb\x84\x66\x66\x64\x44\x64\x66\x46\x86\x8c\xce\xee\xff\xff\xee\xee\xee\xee\xee\xee\xee\xa4\x48\x87\x46\x8c\xee\xca\xab\xbb\xa8\x88\x88\xca\xb8\x88\x66\x78\x8a\xab\xbb\xba\x7a\x87\x44\x47\x8a\xab\xbb\xba\xaa\xaa\xbc\xbe\xee\xcb\xaa\xce\xce\xee\xee\xee\xeb\xa8\x44\x64\x44\x64\x66\x44\x66\x64\x68\x7a\xbe\xee\xff\xfe\xee\xee\xee\xee\xee\xee\xee\xb4\x68\xa8\x66\x7b\xee\xeb\xab\xba\xa8\xaa\x88\xbb\xba\x87\x67\x88\x8a\xbb\xbb\xa8\x8b\xa7\x66\x67\x8a\xaa\xab\xaa\xaa\xaa\xbb\xee\xcc\xbc\xbb\xcc\xce\xee\xee\xcb\xba\xa4\x46\x44\x44\x67\x67\x67\x77\x67\x77\x78\xac\xee\xff\xfe\xee\xec\xcc\xee\xee\xee\xec\xc4\x68\xa8\x76\x7a\xce\xeb\xbb\xba\x8a\x88\x88\xbb\xba\xa8\x77\x88\xaa\xbb\xbc\xa8\xab\xa7\x66\x47\x8a\xaa\xab\xab\xaa\xaa\xbe\xec\xec\xba\xbb\xbc\xce\xee\xee\xcb\xa8\x74\x74\x44\x44\x44\x44\x44\x44\x24\x24\x77\x8b\xef\xff\xff\xee\xec\xcc\xce\xee\xee\xee\xa4\x68\xaa\x87\x78\xce\xec\xbb\xaa\xa8\xa8\xa8\xbb\xba\x88\x77\x88\xaa\xbb\xbb\x88\xbc\xa8\x64\x67\x8a\xaa\xba\xba\xaa\xab\xce\xcc\xcb\xba\xcb\xbc\xee\xee\xee\xcb\xa8\x26\x42\x11\x11\x12\x21\x11\x11\x11\x11\x26\x8b\xee\xef\xff\xee\xee\xcc\xcc\xce\xee\xce\xa4\x67\xaa\xa7\x78\xae\xec\xcb\xaa\x88\xa8\x88\xbb\xba\xa8\x78\x88\xaa\xbc\xba\x7a\xcc\xa8\x66\x46\x8a\xaa\xaa\xaa\xaa\xbc\xcc\xcc\xcc\xaa\xbb\xbc\xee\xee\xcc\xcb\x88\x44\x11\x11\x11\x11\x11\x11\x11\x11\x11\x22\x8a\xce\xef\xff\xfe\xee\xcc\xcc\xce\xec\xce\xa4\x68\x8a\xa8\x78\x8c\xee\xcc\xa8\xaa\x8a\x88\xbb\xbb\xa8\x88\x8a\xaa\xbb\xb8\x8c\xcb\xa8\x66\x46\x8a\xaa\xab\xaa\xaa\xcb\xbb\xcc\xcb\xaa\xab\xbc\xcc\xec\xee\xeb\xa7\x42\x11\x11\x11\x11\x11\x11\x11\x11\x11\x16\x7a\xce\xff\xfe\xff\xee\xcb\xab\xcc\xcc\xce\xb7\x67\x8a\x88\x78\x8b\xee\xee\xba\x8a\x88\x8a\xbb\xbb\xaa\x88\x8a\xab\xbb\xb7\xac\xcb\xa8\x76\x47\x8a\xab\xaa\xaa\xaa\xbb\xbb\xcc\xba\xaa\xab\xbc\xce\xcc\xcc\xcb\x87\x44\x11\x11\x11\x12\x11\x11\x11\x11\x12\x44\x8a\xce\xef\xef\xef\xee\xec\xba\xac\xcc\xce\xb7\x66\x88\xa8\x87\x8b\xcc\xec\xca\xa8\xaa\x88\xbb\xbb\xba\x88\xaa\xbb\xab\xa7\xcc\xcb\xa8\x76\x66\x8a\xaa\xaa\xaa\xab\xbb\xbb\xbb\xaa\xbb\xcb\xce\xce\xec\xbb\xaa\xa8\x64\x11\x11\x11\x24\x11\x11\x44\x11\x66\x44\x6a\xce\xff\xef\xee\xfe\xec\xcb\xbb\xbb\xbc\xc7\x76\x78\xaa\xa8\x8b\xcc\xcc\xca\xa8\xa8\x8a\xbb\xbb\xba\x88\xaa\xbb\xba\x8a\xcc\xcb\xaa\x87\x66\x8a\xaa\x88\x88\x8a\xaa\xaa\xa8\x88\xaa\xbb\xec\xcc\xec\xcc\xbc\xca\x77\x66\x64\x21\x12\x11\x11\x48\x76\x84\x46\x7b\xce\xee\xee\xfe\xec\xcb\xcb\xbb\xcc\xce\xb8\x78\x78\xaa\xa8\x8b\xce\xcc\xca\xaa\x8a\x88\xbb\xbc\xba\xaa\xaa\xba\xaa\x8c\xcc\xcc\xba\x88\x76\x88\xaa\xa8\x88\x8a\xaa\xaa\xa8\xaa\xaa\xac\xec\xcc\xcc\xcc\xeb\xa8\x87\x76\x46\x64\x11\x11\x11\x12\x24\x44\x47\x8a\xbc\xee\xee\xfe\xfe\xbb\xbb\xac\xce\xce\xc7\x78\x88\xaa\xa8\x8a\xce\xec\xeb\xaa\x8a\x8a\xbb\xbb\xba\xaa\xab\xba\xa8\xac\xcc\xcc\xba\x88\x76\x8a\xa8\x88\xa8\x8a\x8a\xa8\x8a\xaa\xaa\xbe\xee\xee\xcc\xcc\xba\xa8\x88\x44\x24\x42\x11\x12\x11\x11\x12\x44\x67\x8a\xbe\xee\xee\xee\xee\xcb\xcb\xbc\xcc\xcc\xc8\x78\x8a\xaa\xaa\x88\xae\xce\xec\xa8\xa8\xa8\xbb\xbb\xaa\xaa\xbb\xaa\xa7\xbb\xcc\xee\xca\xa8\x77\x8a\x88\xa8\xa8\x8a\x88\x88\xaa\x8a\xaa\xbc\xcc\xcb\xba\xbb\xaa\xaa\x88\x66\x22\x12\x11\x11\x11\x11\x11\x44\x47\x8a\xbc\xce\xce\xef\xef\xcc\xcc\xee\xee\xcc\xb8\x88\x8a\xcc\xba\xa8\x8c\xec\xee\xa8\xa8\xa8\xbb\xbb\xab\xbb\xba\xaa\x8a\xcc\xce\xee\xba\x88\x86\x8a\xa8\xa8\x88\x88\x88\x88\x88\x88\xaa\xbc\xcc\xba\xab\xbb\xab\xaa\x78\x66\x44\x21\x11\x12\x11\x21\x24\x44\x48\x8a\xaa\xbc\xee\xee\xef\xcb\xcc\xce\xee\xcc\xa8\x88\x88\xac\xca\xa8\x78\xce\xcc\xb8\xaa\xaa\xbb\xbb\xbb\xbb\xba\xa8\x7c\xcc\xee\xee\xba\xa8\x87\x8a\x88\x88\xaa\x88\x88\x88\xaa\xaa\xaa\xcc\xcc\xba\x88\x8a\xaa\x88\xaa\x87\x64\x42\x44\x12\x12\x44\x44\x44\x76\x78\xbb\xce\xee\xee\xef\xcb\xcc\xee\xec\xcc\xaa\xa8\x88\x8c\xec\xaa\x87\xae\xce\xba\xaa\x8a\xbb\xbb\xbb\xab\xaa\x87\xbc\xbe\xee\xee\xeb\xaa\x88\x88\x88\xaa\xaa\xa8\x88\xaa\xaa\xa8\xaa\xcc\xcc\xcc\xbb\xaa\x8a\xaa\xa8\x87\x86\x64\x44\x41\x12\x44\x44\x44\x68\x48\xab\xcc\xee\xee\xee\xcb\xcc\xce\xeb\xbb\xaa\xaa\x8a\xbe\xcc\xba\xa8\x77\xae\xcc\xaa\x8a\xbb\xbb\xba\xaa\x88\x7b\xcc\xce\xee\xee\xec\xba\x88\x88\x8a\xaa\xaa\xa8\x88\xaa\x88\x8a\xaa\xbb\xcb\xba\xbb\xaa\xaa\xba\x88\xa7\x66\x64\x44\x42\x14\x44\x44\x44\x66\x8a\xab\xec\xee\xee\xee\xbb\xec\xcc\xcc\xca\xaa\xaa\xab\xee\xec\xba\xaa\xa8\x68\xcb\xba\xaa\xbb\xbb\xaa\xa8\x88\xbc\xbc\xce\xee\xee\xee\xba\x88\x88\x88\xa8\xaa\xaa\x88\x88\x88\xaa\x8a\xab\xca\xaa\xaa\xba\x8a\xaa\x88\x86\x66\x44\x44\x62\x24\x44\x44\x44\x67\x8a\xaa\xbb\xbc\xee\xee\xcc\xcc\xbc\xcb\xbb\xaa\xaa\xac\xee\xee\xcb\xaa\xaa\xa8\xac\xaa\x8a\xbb\xba\xa8\x88\x6a\xcb\xce\xee\xee\xee\xec\xba\xa8\x88\x88\x88\xaa\xa8\x88\xa8\x8a\x87\x8a\xac\xba\xab\xaa\xaa\xaa\xa8\xa7\x66\x46\x44\x46\x44\x22\x44\x44\x46\x68\x88\xbc\xbb\xee\xee\xee\xcc\xcb\xbb\xbb\xaa\xaa\xaa\xbc\xee\xee\xeb\xaa\xaa\xab\xbb\xaa\xaa\xbb\xba\xaa\x78\xac\xcc\xce\xee\xee\xee\xec\xcb\xaa\x88\x88\x88\x8a\x88\x8a\x88\xa7\x77\x8a\x8b\xbb\xba\xa8\x88\x8a\x78\x88\x77\x74\x66\x46\x44\x44\x44\x44\x46\x64\x8b\xab\xce\xce\xee\xeb\xcc\xeb\xba\xba\xba\xbb\xce\xee\xef\xfe\xec\xba\xa8\xaa\xaa\x8a\x8a\xbb\xaa\xba\xbb\xcb\xcc\xee\xee\xee\xee\xee\xec\xaa\xa8\x88\x88\x88\x88\xa8\x8b\x87\x78\x88\xaa\xbc\xbb\xaa\xaa\xaa\xa8\xa8\x67\x64\x66\x44\x66\x44\x64\x44\x44\x76\x8a\xba\xbc\xcc\xee\xeb\xce\xcc\xcb\xab\xcb\xcc\xee\xff\xef\xfe\xec\xca\xaa\xaa\xaa\xaa\xaa\xbb\xbb\xcb\xcb\xbc\xcc\xee\xee\xee\xee\xee\xcc\xaa\xaa\x88\x88\x88\x88\x88\xaa\x88\x88\x6a\x88\xba\xba\xaa\xaa\xa8\x88\x87\x68\x67\x77\x64\x68\x47\x77\x64\x84\x86\x8a\xab\xab\xcc\xee\xca\xce\xeb\xbb\xbc\xcc\xcc\xce\xef\xff\xff\xfe\xec\xaa\xaa\x8a\xaa\x8a\xbb\xbb\xbb\xbb\xcc\xcc\xee\xee\xee\xee\xee\xec\xaa\xaa\x88\x88\x88\x88\x8a\xa8\x88\x87\x86\x8a\xaa\xaa\xaa\x88\x88\x68\x86\x77\x76\x77\x86\x64\x44\x66\x76\x86\x87\x8a\xab\xba\xcc\xeb\xab\xce\xec\xcb\xcc\xbc\xce\xee\xee\xff\xff\xff\xee\xca\xaa\xaa\xa8\xaa\xbb\xbb\xbb\xbb\xbc\xcc\xee\xee\xee\xee\xee\xec\xba\xaa\xa8\x88\x88\x88\x8a\x88\x8a\x88\x44\x88\xaa\xaa\xa8\x88\x88\x68\x87\x66\x86\x86\x62\x11\x11\x12\x44\x77\x78\x68\x8a\xab\xcc\xc7\x7b\xce\xec\xcb\xcc\xcc\xee\xee\xee\xff\xff\xfe\xee\xeb\xaa\xaa\xa8\xaa\xbb\xbb\xbc\xbc\xcc\xcc\xee\xee\xee\xee\xee\xec\xca\xaa\xa8\x88\x88\x88\x8a\x8a\xaa\x86\x42\x86\x8a\x8a\xaa\xa8\xa8\xa7\x86\x76\x84\x64\x12\x11\x11\x11\x11\x46\x47\x67\x88\xaa\xbe\x67\x7a\xbc\xee\xec\xcc\xcc\xee\xee\xef\xef\xff\xef\xee\xcb\xaa\xaa\x8a\xaa\xbb\xbb\xbc\xbb\xbc\xce\xee\xee\xee\xee\xee\xee\xcb\xaa\xa8\x88\x88\x88\x88\x8a\xaa\x84\x44\x44\x87\xa8\x8a\x88\x87\x67\x76\x74\x72\x22\x11\x11\x11\x11\x11\x24\x47\x46\x78\x8a\xa8\x77\x8a\xbb\xee\xee\xec\xce\xee\xee\xee\xef\xff\xff\xec\xca\xaa\xaa\xaa\x8a\xbb\xbb\xcb\xbc\xbc\xce\xee\xee\xee\xee\xee\xee\xcb\xaa\xaa\x88\x88\x88\x88\xaa\xaa\x86\x44\x41\x66\x78\x88\xa8\x77\x66\x87\x62\x41\x11\x11\x11\x11\x11\x11\x24\x46\x66\x77\x77\x84\x77\x8a\xab\xcc\xee\xcc\xec\xee\xee\xef\xff\xff\xff\xee\xcb\xaa\xaa\xaa\xaa\xbb\xbb\xbc\xbc\xcc\xee\xee\xee\xee\xee\xee\xec\xcc\xaa\xaa\x88\x88\x88\x88\xaa\xaa\x86\x47\x22\x44\x47\x78\x88\x88\x77\x64\x42\x22\x11\x11\x11\x11\x11\x12\x22\x46\x74\x44\x66\x64\x88\x8a\xab\xce\xce\xcc\xec\xee\xee\xee\xef\xff\xff\xfe\xeb\xba\xaa\x8a\x8a\xbb\xbb\xcb\xcc\xcc\xee\xee\xee\xee\xee\xec\xec\xcb\xba\xaa\xaa\x88\x88\x8a\xba\xa8\x86\x67\x14\x44\x16\x46\x87\x66\x44\x42\x42\x24\x21\x21\x11\x11\x11\x22\x24\x46\x77\x41\x44\x64\x88\xab\xbc\xcc\xcc\xcc\xce\xee\xef\xef\xff\xff\xff\xff\xec\xba\xaa\xaa\xaa\xbb\xbb\xcb\xbc\xcc\xee\xee\xee\xee\xec\xec\xce\xcb\xba\xaa\x8a\x88\x88\xaa\xba\xa8\x86\x67\x24\x42\x14\x14\x84\x12\x44\x44\x44\x24\x22\x42\x11\x12\x22\x22\x44\x44\x78\x84\x44\x66\xaa\xbc\xcc\xce\xcc\xcc\xee\xee\xee\xfe\xfe\xff\xff\xff\xfe\xca\xaa\x8a\x8a\xbb\xbb\xcb\xcc\xcc\xee\xee\xee\xee\xcc\xec\xce\xcc\xba\xaa\xaa\x88\x8a\xaa\xaa\x88\x77\x77\x24\x42\x14\x11\x67\x14\x44\x44\x44\x44\x44\x44\x12\x12\x22\x24\x44\x66\x68\xa7\x44\x67\xbb\xbb\xcc\xec\xcc\xce\xee\xee\xee\xee\xef\xff\xff\xff\xfe\xca\xaa\xaa\xaa\xbb\xbb\xcc\xcc\xce\xee\xee\xee\xce\xec\xce\xcc\xcc\xba\xaa\xaa\xa8\xaa\xaa\xaa\xa8\x87\x77\x44\x42\x26\x11\x24\x24\x44\x44\x44\x44\x44\x44\x22\x22\x42\x44\x44\x67\x77\x8a\x64\x68\xbb\xbc\xcc\xcc\xcc\xce\xee\xee\xee\xee\xee\xef\xff\xff\xfe\xca\xaa\xaa\x8a\xbb\xcb\xcc\xce\xee\xee\xee\xee\xec\xcc\xcc\xcc\xbb\xbb\xaa\xaa\x8a\xa8\xaa\xaa\xaa\x88\x78\x66\x42\x16\x11\x11\x67\x64\x66\x66\x66\x64\x66\x21\x24\x44\x44\x46\x67\x77\x8a\x84\x48\xbc\xcc\xcc\xcc\xec\xee\xee\xee\xee\xee\xff\xff\xff\xff\xff\xeb\xaa\xaa\xaa\xbb\xbb\xbc\xce\xee\xee\xee\xee\xec\xec\xcc\xcc\xbb\xbb\xaa\xaa\xaa\x88\x88\xaa\xaa\x88\x88\x76\x61\x16\x21\x11\x87\x66\x66\x66\x66\x74\x66\x41\x44\x44\x46\x66\x77\x77\x8a\x84\x6a\xbb\xbc\xbb\xcc\xce\xee\xee\xee\xee\xee\xee\xff\xff\xff\xff\xec\xaa\xa8\xaa\xbb\xbc\xcc\xee\xee\xee\xee\xec\xcc\xcc\xcc\xbb\xbb\xbb\xaa\xaa\xaa\x88\x88\x8a\x88\x88\x88\x86\x71\x24\x41\x11\x78\x76\x77\x67\x76\x74\x66\x42\x44\x44\x46\x67\x67\x77\x7b\x46\x6a\xbb\xbb\xbc\xcc\xce\xee\xee\xee\xee\xee\xef\xfe\xff\xff\xff\xec\xaa\xaa\xaa\xbb\xbb\xcc\xee\xee\xee\xee\xee\xec\xcc\xcb\xcb\xcb\xbb\xab\xaa\xba\xaa\x88\x88\x88\xa8\x88\x87\x72\x14\x42\x11\x48\x77\x77\x67\x77\x76\x77\x62\x44\x66\x67\x67\x77\x76\xa8\x46\x6b\xbb\xcc\xbc\xcc\xce\xee\xee\xee\xee\xee\xee\xfe\xff\xff\xff\xfe\xba\xaa\xaa\xbb\xcb\xce\xee\xee\xee\xee\xee\xcc\xcc\xcb\xbb\xcb\xbb\xbb\xaa\xaa\x88\x88\xa8\x88\x88\x88\x87\x74\x24\x24\x12\x17\xa8\x87\x78\x78\x86\x77\x72\x44\x66\x67\x77\x77\x77\xa8\x66\x7b\xbc\xcb\xcc\xce\xee\xee\xee\xee\xee\xee\xee\xef\xff\xff\xff\xff\xca\xaa\xaa\xbb\xbc\xcc\xee\xee\xee\xee\xec\xec\xcc\xcc\xbb\xcb\xbc\xba\xba\xaa\xa8\x88\xa8\x88\x88\x88\x88\x74\x24\x14\x24\x42\x88\x88\x88\x88\x88\x88\x84\x46\x77\x77\x77\x77\x7a\xa6\x74\x8b\xbc\xcc\xcc\xce\xee\xee\xee\xee\xee\xee\xee\xef\xef\xff\xff\xff\xea\xaa\xaa\xbb\xcc\xce\xee\xee\xee\xee\xec\xec\xcc\xbc\xbc\xbc\xcb\xbb\xba\xaa\xaa\x88\xa8\x88\x88\xa8\x88\x86\x24\x22\x24\x42\x6a\xaa\x88\x88\x88\x88\x86\x46\x77\x78\x78\x77\x7a\x77\x67\xaa\xbc\xcc\xcc\xee\xee\xee\xee\xee\xee\xee\xee\xff\xef\xff\xff\xff\xeb\xaa\xaa\xcb\xbc\xee\xee\xee\xee\xee\xee\xcc\xcc\xcb\xbc\xcb\xcb\xba\xba\xaa\xaa\xa8\xa8\x88\x88\x88\x87\x87\x42\x22\x22\x44\x18\xaa\x8a\x8a\xaa\xaa\xa7\x67\x78\x78\x87\x77\xaa\x86\x68\xaa\xbc\xcc\xce\xee\xee\xee\xee\xee\xee\xfe\xfe\xef\xff\xff\xff\xff\xee\xba\xaa\xbb\xcc\xee\xee\xee\xee\xee\xce\xcc\xcc\xcb\xcc\xcb\xbb\xbb\xba\xaa\xaa\x88\x88\x88\x88\x8a\x88\x78\x62\x22\x22\x44\x47\xaa\xba\xaa\xaa\xaa\xa8\x67\x78\x78\x88\x77\xb8\xa6\x88\xaa\xcc\xcc\xce\xee\xee\xee\xee\xee\xff\xff\xfe\xff\xef\xff\xff\xff\xee\xca\xaa\xcb\xcc\xee\xee\xee\xee\xee\xce\xcc\xcc\xcb\xcc\xbb\xbb\xbb\xaa\xaa\xaa\xa8\x88\x88\x78\x8a\xa8\x77\x76\x21\x22\x44\x42\x7b\xaa\xaa\xaa\xaa\xaa\x77\x88\x87\x87\x6a\xa6\x87\xbb\xcc\xcc\xcc\xcc\xee\xee\xee\xee\xee\xef\xef\xef\xff\xff\xff\xff\xff\xee\xcb\xaa\xbb\xce\xee\xee\xee\xee\xee\xec\xcc\xcc\xcc\xcb\xbc\xcb\xbb\xaa\xaa\xaa\x88\x88\x88\x88\x88\xa8\x88\x76\x42\x22\x44\x42\x4a\xba\xaa\xaa\xaa\xaa\x87\x88\x88\x78\x6b\x46\x66\x8b\xcc\xcc\xcc\xce\xee\xee\xee\xee\xef\xfe\xfe\xff\xfe\xff\xff\xff\xff\xee\xcb\xaa\xcc\xce\xee\xee\xee\xee\xee\xec\xec\xcb\xcc\xcc\xbc\xbb\xbb\xba\xaa\xaa\x8a\x88\x88\x88\x88\x88\x88\x76\x44\x22\x44\x44\x27\xbb\xaa\xaa\xab\xba\x88\x88\x88\x76\x8a\xa6\x26\x8b\xce\xec\xcc\xee\xee\xee\xee\xee\xee\xee\xef\xef\xff\xef\xff\xff\xff\xfe\xca\xaa\xcc\xee\xee\xee\xee\xee\xee\xce\xcc\xcc\xcc\xcb\xcb\xbb\xbb\xaa\xaa\xaa\xaa\x88\x88\x88\x77\x8a\x88\x76\x66\x42\x42\x22\x44\x8c\xbb\xab\xab\xba\xa8\x88\x88\x87\xbb\xc6\x27\x8b\xcc\xec\xcc\xee\xee\xee\xee\xee\xee\xee\xee\xfe\xff\xff\xff\xff\xff\xee\xba\xaa\xcc\xee\xee\xee\xee\xee\xee\xcc\xcc\xcc\xcc\xcc\xbb\xbb\xbb\xaa\xaa\xaa\xaa\x88\x88\x88\x87\x78\x78\x88\x87\x64\x21\x24\x6a\x8a\xbb\xbb\xbb\xba\xa8\x88\x88\x77\xab\x78\x28\x7c\xcc\xec\xec\xee\xee\xee\xee\xee\xee\xee\xee\xee\xef\xff\xff\xff\xff\xfe\xca\xaa\xcc\xce\xee\xee\xee\xee\xee\xce\xcc\xec\xec\xcc\xbb\xbb\xba\xaa\xaa\xaa\xa8\x88\x88\x88\x77\x87\x78\x88\x87\x42\x22\x24\x67\xa7\xcb\xab\xbb\xba\xaa\x88\x88\x78\xba\xa8\x44\x7e\xcc\xce\xce\xee\xee\xee\xfe\xee\xee\xee\xee\xee\xff\xef\xff\xff\xff\xff\xcb\xaa\xce\xee\xee\xee\xee\xee\xee\xec\xee\xee\xec\xcc\xcb\xbb\xaa\xaa\xaa\xaa\x88\x88\x88\x77\x78\x87\x8a\xa8\x78\x44\x12\x44\x74\xa6\xab\xba\xbb\xbb\xaa\xa8\x88\x6a\xa8\x88\x84\x8c\xec\xec\xee\xee\xee\xee\xef\xee\xee\xee\xee\xee\xff\xff\xff\xff\xff\xff\xeb\xaa\xcc\xee\xee\xee\xee\xee\xcc\xcc\xec\xec\xcc\xcb\xbb\xbb\xab\xba\xaa\xaa\x8a\x88\x77\x78\x88\x87\x88\x88\x88\x64\x44\x24\x66\x64\x8b\xbb\xba\xba\xaa\x8a\x88\x7b\x67\x48\x88\xbe\xee\xce\xee\xee\xee\xee\xee\xee\xee\xee\xee\xee\xff\xef\xff\xff\xff\xff\xeb\xaa\xcc\xee\xee\xee\xee\xce\xce\xce\xce\xce\xcc\xcc\xbb\xbb\xba\xba\xaa\xaa\x88\x88\x77\x78\x88\x87\x66\x88\x88\x84\x22\x24\x26\x42\x4c\xbb\xab\xbb\xaa\x88\x88\xa8\x87\x46\x6a\xce\xee\xee\xee\xee\xee\xee\xee\xef\xee\xee\xee\xee\xff\xff\xff\xff\xff\xff\xeb\xaa\xcc\xce\xee\xee\xee\xcc\xce\xcc\xcc\xcc\xcc\xbb\xbb\xbb\xba\xaa\xaa\xaa\x88\x88\x78\x78\x78\x77\x66\x68\x88\x86\x42\x42\x22\x24\x1a\xcb\xab\xab\xaa\xa8\xaa\x88\x84\x24\x8c\xee\xec\xec\xee\xee\xee\xee\xee\xee\xee\xee\xee\xfe\xff\xff\xff\xff\xff\xff\xec\xaa\xbc\xee\xee\xee\xec\xce\xcc\xec\xcc\xcc\xbc\xbc\xbc\xcb\xba\xaa\xaa\xaa\x88\x88\x87\x77\x78\x76\x44\x68\x88\x88\x64\x21\x21\x24\x41\xae\xba\xba\xaa\x88\xaa\x86\x42\x67\xbe\xec\xee\xee\xee\xee\xee\xee\xee\xee\xee\xee\xee\xee\xff\xff\xff\xff\xff\xff\xec\xaa\xcc\xee\xee\xee\xcc\xcc\xcc\xcc\xcc\xcb\xcc\xbc\xbc\xbb\xaa\xaa\xaa\xaa\x88\x88\x87\x86\x78\x84\x46\x67\x78\x88\x86\x44\x11\x11\x11\x28\xce\xcb\xb8\xaa\x74\x42\x26\xab\xee\xcc\xec\xee\xee\xee\xee\xee\xee\xee\xee\xee\xee\xff\xff\xff\xff\xef\xff\xff\xfc\xaa\xcc\xec\xee\xee\xcc\xcc\xcc\xbc\xbb\xcb\xbc\xbb\xbb\xbb\xbb\xab\xaa\xaa\xa8\x88\x87\x76\x77\x64\x46\x66\x87\x78\x88\x76\x42\x11\x11\x11\x17\xab\xbb\x71\x11\x24\x47\xae\xee\xec\xcc\xce\xee\xee\xee\xee\xee\xee\xee\xee\xfe\xfe\xfe\xff\xff\xff\xff\xff\xfe\xba\xcc\xec\xee\xec\xec\xcc\xcc\xcb\xcb\xcb\xbb\xbb\xcb\xbb\xbb\xba\xaa\xaa\xa8\x88\x88\x67\x76\x44\x46\x46\x77\x77\x88\x88\x64\x41\x11\x11\x11\x11\x12\x11\x11\x24\x7b\xee\xec\xcb\xcc\xee\xee\xee\xee\xee\xee\xee\xee\xee\xee\xfe\xff\xfe\xfe\xff\xff\xff\xfe\xba\xcc\xee\xee\xec\xcc\xbc\xbc\xcb\xcb\xbb\xcb\xbb\xcb\xbb\xbb\xba\xaa\xaa\xa8\x88\x77\x77\x74\x44\x46\x46\x76\x76\x8a\xa8\x88\x64\x42\x11\x11\x11\x11\x11\x14\x68\xae\xee\xec\xbb\xbc\xcc\xee\xee\xee\xee\xee\xee\xee\xee\xee\xee\xee\xfe\xfe\xff\xff\xff\xfe\xca\xcc\xee\xee\xec\xcb\xcb\xcc\xcb\xcb\xcb\xcb\xbb\xbb\xbb\xba\xaa\xaa\xaa\x88\x88\x87\x78\x64\x44\x44\x66\x77\x84\x68\xa8\x88\x86\x64\x22\x22\x12\x22\x24\x46\xab\xcc\xec\xcc\xbb\xbc\xec\xee\xee\xee\xee\xee\xee\xee\xee\xee\xee\xfe\xfe\xee\xff\xff\xff\xff\xcb\xce\xee\xec\xcc\xcb\xbc\xcc\xcc\xcb\xcb\xbc\xbb\xbb\xab\xbb\xba\xaa\xaa\x88\x88\x78\x87\x44\x46\x44\x66\x77\x86\x48\x88\x88\x78\x76\x44\x44\x24\x44\x68\x7a\xbb\xce\xcc\xab\xab\xbc\xcc\xee\xee\xee\xee\xee\xee\xee\xee\xee\xee\xee\xee\xfe\xef\xff\xff\xfe\xeb\xce\xee\xcc\xcc\xbb\xcc\xcc\xbc\xbb\xbb\xba\xaa\xba\xbb\xaa\xaa\xaa\xaa\x88\x88\x88\x86\x44\x76\x44\x47\x76\x88\x66\x68\xa8\x88\x88\x77\x74\x66\x88\x88\xaa\xbc\xcc\xab\xaa\xba\xbb\xcc\xee\xee\xee\xee\xee\xee\xee\xee\xee\xee\xee\xef\xef\xff\xff\xff\xff\xec\xcc\xee\xec\xcc\xcc\xcc\xcc\xbc\xbb\xbb\xab\xab\xaa\xaa\xaa\xaa\xaa\xa8\x88\x88\x88\x74\x46\x76\x44\x47\x86\x68\x86\x47\x88\x88\x88\x88\x88\x88\x8a\x88\xaa\xbb\xbb\xaa\xab\xab\xbc\xcc\xce\xee\xee\xee\xee\xee\xee\xee\xee\xee\xef\xef\xef\xff\xff\xff\xff\xec\xce\xee\xce\xcc\xbb\xbc\xcb\xbc\xbb\xbb\xbb\xab\xaa\xaa\xaa\xaa\xaa\xa8\x88\x88\x88\x64\x67\x76\x44\x67\x87\x67\x87\x64\x68\x88\x88\x88\x88\x88\x8a\x8a\xaa\xab\xbb\xaa\xab\xab\xbb\xcc\xcc\xee\xee\xee\xee\xee\xee\xee\xee\xee\xfe\xff\xff\xff\xff\xff\xff\xff\xce\xee\xcc\xcc\xbb\xbb\xcc\xbb\xcc\xbb\xbb\xab\xaa\xaa\xaa\xaa\xaa\xaa\x88\x88\x87\x44\x78\x76\x64\x67\x88\x77\x88\x74\x46\x78\x88\x88\x88\x88\xaa\xaa\xa8\xab\xba\xaa\xaa\xba\xcc\xcc\xec\xce\xee\xce\xee\xee\xee\xee\xee\xee\xee\xfe\xff\xff\xff\xff\xff\xff\xce\xce\xcc\xbb\xbb\xbb\xcb\xbc\xbc\xbb\xbb\xbb\xaa\xba\xaa\xaa\xaa\xaa\x88\x8a\x86\x47\x87\x77\x66\x67\x78\x87\x78\x87\x44\x67\x88\x88\x88\x87\x88\x8a\xa8\xab\xba\xaa\xaa\xba\xbc\xcc\xee\xce\xec\xce\xee\xee\xee\xee\xee\xee\xef\xef\xff\xff\xff\xff\xff\xff\xce\xcc\xcb\xbb\xaa\xbb\xcc\xcb\xbb\xbb\xbb\xbb\xba\xaa\xaa\xaa\xaa\xaa\xaa\xa8\x64\x78\x88\x78\x77\x67\x88\x88\x88\x78\x86\x46\x88\x88\x78\x87\x78\x8a\xa8\xaa\xba\xaa\xaa\xab\xab\xcc\xcc\xec\xee\xec\xee\xee\xee\xee\xee\xee\xee\xee\xff\xff\xff\xff\xff\xff\xce\xcc\xcb\xba\xaa\xbb\xbb\xbb\xcc\xbc\xbc\xbb\xba\xaa\xaa\xaa\xaa\xaa\xaa\xa6\x46\x88\x88\x88\x77\x77\x88\x88\x88\x88\x88\x66\x68\x88\x88\x87\x78\x8a\xa8\xaa\xaa\xaa\xaa\xab\xba\xcc\xcc\xcc\xec\xec\xee\xee\xee\xee\xee\xee\xee\xff\xef\xff\xff\xff\xff\xff\xce\xcc\xcb\xbb\xaa\xbb\xcb\xcb\xcb\xcc\xbb\xbb\xaa\xba\xaa\xaa\xaa\xaa\xaa\x84\x48\x88\x88\x87\x88\x88\x88\x88\x88\x88\x88\x88\x7a\x88\x88\x87\x78\x8a\xa8\xaa\xaa\xab\xaa\xaa\xbb\xbc\xcc\xcc\xec\xec\xee\xee\xee\xee\xee\xee\xee\xef\xef\xff\xff\xff\xff\xff")
        self.fbuf = framebuf.FrameBuffer(data, 128, 128, framebuf.GS4_HMSB)
        
        #Init music
        song = '0 A4 2 0 1;0 C5 2 0 1;0 E5 2 0 1;2 B4 2 0 1;4 C5 3 0 1;7 B4 1 0 1;10 C5 2 0 1;12 G4 3 0 1;16 G4 2 0 1;16 B4 2 0 1;16 D5 2 0 1;18 B4 2 0 1;20 C5 3 0 1;23 B4 1 0 1;26 C5 2 0 1;28 G4 3 0 1;32 G4 2 0 1;32 B4 2 0 1;32 D5 2 0 1;34 B4 2 0 1;36 C5 3 0 1;39 B4 1 0 1;42 C5 2 0 1;44 G4 3 0 1;48 A4 2 0 1;48 C5 2 0 1;48 E5 2 0 1;50 B4 2 0 1;52 C5 3 0 1;55 B4 1 0 1;58 C5 2 0 1;60 G4 2 0 1;62 G5 1 0 1;63 G5 1 0 1;64 A4 2 0 1;64 C5 2 0 1;64 E5 2 0 1;66 B4 2 0 1;68 C5 3 0 1;71 B4 1 0 1;74 C5 2 0 1;76 G4 3 0 1;80 G4 2 0 1;80 B4 2 0 1;80 D5 2 0 1;82 B4 2 0 1;84 C5 3 0 1;87 B4 1 0 1;90 C5 2 0 1;92 G4 3 0 1;96 G4 2 0 1;96 B4 2 0 1;96 D5 2 0 1;98 B4 2 0 1;100 C5 3 0 1;103 B4 1 0 1;106 C5 2 0 1;108 G4 3 0 1;112 A4 2 0 1;112 C5 2 0 1;112 E5 2 0 1;114 B4 2 0 1;116 C5 3 0 1;119 B4 1 0 1;122 C5 2 0 1;124 G4 2 0 1;126 G5 1 0 1;127 G5 1 0 1;128 A4 2 0 1;128 C5 2 0 1;128 E5 2 0 1;130 B4 2 0 1;132 C5 3 0 1;135 B4 1 0 1;138 C5 2 0 1;140 G4 3 0 1;144 G4 2 0 1;144 B4 2 0 1;144 D5 2 0 1;146 B4 2 0 1;148 C5 3 0 1;151 B4 1 0 1;154 C5 2 0 1;156 G4 3 0 1;160 G4 2 0 1;160 B4 2 0 1;160 D5 2 0 1;162 B4 2 0 1;164 C5 3 0 1;167 B4 1 0 1;170 C5 2 0 1;172 G4 3 0 1;176 A4 2 0 1;176 C5 2 0 1;176 E5 2 0 1;178 B4 2 0 1;180 C5 3 0 1;183 B4 1 0 1;186 C5 2 0 1;188 G4 2 0 1;190 G5 1 0 1;191 G5 1 0 1;192 F4 2 0 1;192 A4 2 0 1;192 C5 2 0 1;192 E5 2 0 1;194 B4 2 0 1;196 C5 3 0 1;199 B4 1 0 1;202 C5 2 0 1;204 G4 3 0 1;208 G4 2 0 1;208 B4 2 0 1;208 D5 2 0 1;210 B4 2 0 1;212 C5 3 0 1;215 B4 1 0 1;218 C5 2 0 1;220 G4 3 0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
            
        #Render display
        self.display.show()
        
        #Wait a fixed amount of time between ticks (independent of time taken to calculate stuff in tick())
        while (utime.ticks_us() - start_time < 40000):
            pass
