james1236/pico-foldable/creations/demo.py

from buzzer_music import music
import utime
import _thread

musicPlaying = False
mySong = None

def musicThread():
    global mySong
    global musicPlaying
    
    while True:
        utime.sleep(0.04)
        if (not musicPlaying):
            mySong.stop()
            del mySong
            break
        
        try:
            mySong.tick()
        except Exception:
            pass

#Optional metadata for main menu
class description:
    name = "Demo"
    #32x32 Horizonal - 1 bit per pixel (https://javl.github.io/image2cpp/)
    thumbnail = bytearray(b"\x00\x00\x00\x00\x00\x00\x00\x00\x00\x00\x00\x00\x0e\x18\xd8\x60\x09\x21\x24\x90\x09\x21\x24\x90\x09\x39\x24\x90\x09\x21\x04\x90\x09\x21\x04\x90\x09\x21\x04\x90\x0e\x19\x04\x60\x00\x00\x00\x00\x00\x00\x00\x00\x00\x03\xc0\x00\x00\x13\xc8\x00\x00\x3e\x7e\x00\x00\xfe\x7f\x00\x00\x61\x86\x00\x00\x77\xee\x00\x01\xee\x77\x80\x01\xcc\x33\x80\x01\xcc\x33\x80\x01\xee\x77\x80\x00\x77\xee\x00\x00\x61\x86\x00\x00\xfe\x7f\x00\x00\x7e\x7e\x00\x00\x13\xc8\x00\x00\x03\xc0\x00\x00\x00\x00\x00\x00\x00\x00\x00\x00\x00\x00\x00")

#Required class named 'creation'
class creation:
    def __init__(self, display, controller, *args): #Required init method in creation class
        global mySong
        global musicPlaying
        self.frame = 0
        self.display = display
        self.controller = controller
        
        #Init music
        # song = '2 A4 1 32;0 G4 1 32;2 D4 1 32;4 G4 1 32;8 F#4 1 32;10 C#4 1 32;12 A3 1 32;14 E4 1 32;18 F#4 1 32;22 D4 1 32;24 E4 1 32;26 D4 1 32;9 E4 1 32;8 D4 1 32;10 F#3 1 32;7 B3 1 32;16 G3 1 32;18 D4 1 32;20 G3 1 32;22 A3 1 32;24 E3 1 32;28 F#3 1 32;23 F#3 1 32;28 F#4 1 32;30 A4 1 32;30 A3 1 32;26 B3 1 32;30 D4 1 32;34 A4 1 32;32 G4 1 32;34 D4 1 32;36 G4 1 32;40 F#4 1 32;42 C#4 1 32;44 A3 1 32;46 E4 1 32;50 F#4 1 32;54 D4 1 32;56 E4 1 32;58 D4 1 32;41 E4 1 32;40 D4 1 32;42 F#3 1 32;39 B3 1 32;48 G3 1 32;50 D4 1 32;52 G3 1 32;54 A3 1 32;56 E3 1 32;60 F#3 1 32;55 F#3 1 32;60 F#4 1 32;62 A4 1 32;62 A3 1 32;58 B3 1 32;62 D4 1 32;79 A#7 1 7;122 C#7 1 7;80 F#7 1 7 32;64 D5 1 32;65 B4 1 32;70 B4 1 32;80 B4 1 32;84 B4 1 32;80 G5 1 32;64 D6 1 32;72 C#6 1 32;64 F#5 1 32;72 F#5 1 32;88 E5 1 32;89 G5 1 32;90 B5 1 32;91 C#6 1 32;94 C#6 1 32;92 F#6 1 32;96 D5 1 32;97 B4 1 32;102 B4 1 32;112 B4 1 32;116 B4 1 32;112 G5 1 32;96 D6 1 32;104 C#6 1 32;96 F#5 1 32;104 F#5 1 32;120 E5 1 32;121 G5 1 32;122 B5 1 32;123 C#6 1 32;126 C#6 1 32;124 F#6 1 32;98 F#6 1 32;100 E6 1 32;106 A5 1 32;108 C#6 1 32;110 F#5 1 32;102 D6 1 32;114 E6 1 32;116 F#6 1 32;118 B6 1 32;120 G6 1 32;123 A6 1 32;126 B6 1 32;83 A6 1 32;113 B6 1 32;90 B6 1 32;66 A4 1 32;64 G4 1 32;66 D4 1 32;68 G4 1 32;72 F#4 1 32;74 C#4 1 32;76 A3 1 32;78 E4 1 32;82 F#4 1 32;86 D4 1 32;88 E4 1 32;90 D4 1 32;73 E4 1 32;72 D4 1 32;74 F#3 1 32;71 B3 1 32;80 G3 1 32;82 D4 1 32;84 G3 1 32;86 A3 1 32;88 E3 1 32;92 F#3 1 32;87 F#3 1 32;92 F#4 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
1 43 5;177.04563903808594 B4 1 43 5;178.02560424804688 D#5 1 43 5;178.925048828125 F#5 1 43 5;181.03575134277344 D#5 1 43 5;182.0840606689453 F#5 1 43 5;136.06680297851562 B6 1 43 5;137.9354705810547 D7 1 43 5;188 A6 1 43 5'
        mySong = music(song,True,4)
        musicPlaying = True;

        #Run music on second thread
        musicThreadInstance = _thread.start_new_thread(musicThread, ())
        
    def close(self): #Optional, called by main.py when it must exit back to main menu
        global musicPlaying
        musicPlaying = False
    
    def tick(self): #Required, called by main.py in a loop
        start_time = utime.ticks_us()
        self.frame = self.frame + 1
        
        #Demo graphics
        self.display.fill(0)
        self.display.text(str(self.frame),2,2)
        self.display.fill_rect(self.frame % (self.display.width-1),self.frame % self.display.height,10,10,1)
        self.display.stroke_rect((self.frame+64) % (self.display.width-1),(self.frame+64) % self.display.height,10,10,1)
        self.display.stroke_rect(0,0,self.display.width,self.display.height,1)
        
        #Read joystick input and use it to scroll graphics
        joy = self.controller.readJoystick()
        if (joy[2]):
            self.display.scroll(int(joy[0]),int(joy[1]))
            
        #Render display
        self.display.show()
        
        #Wait a fixed amount of time between ticks (independent of time taken to calculate stuff in tick())
        while (utime.ticks_us() - start_time < 40000):
            pass
